AIWerkstatt/SensorBox/1-CAD/CAD.odt

CAD Design

Our instructions are intended to be used with our YouTube videos that illustrate the different steps. For the CAD Design watch: “ (https://youtu.be/I4eepCoYUTw)How to build the SensorBox – 3D Print (https://youtu.be/I4eepCoYUTw)” (https://youtu.be/I4eepCoYUTw).

We used FreeCAD (https://www.freecadweb.org/) for the design of our SensorBox. We saved our CAD designs in the folder Design in FreeCAD’s native .FCStd file format. Designs for re-use were exported and imported as .step files. We exported our designs as .stl files into the folder STL-files for 3D printing.

# FreeCAD

Take a look at the software setup section for how to set up your host computer.

Download FreeCAD

Firefox: https://www.freecadweb.org/

> Click Download now

> Click Linux 64-Bit AppImage

~/Download/FreeCAD_0.18-16146-rev1-Linux-Conda_Py3Qt5_glibc2.12-x86_64.AppImage

Ubuntu: Right-Click on FreeCAD_0.18-16146-rev1-Linux-Conda_Py3Qt5_glibc2.12-x86_64.AppImage and select Properties

> Select Permissions

> Check Allow executing file as program

An already downloaded copy can be found here:

sw/FreeCAD_0.18-16146-rev1-Linux-Conda_Py3Qt5_glibc2.12-x86_64.AppImage

Run FreeCAD

Ubuntu: Double-Click on sw/FreeCAD_0.18-16146-rev1-Linux-Conda_Py3Qt5_glibc2.12-x86_64.AppImage

# Design

The design consists of two (2) major components: a) sensors & processing board with (almost) all the electronics and b) the cover that includes an integrated display, a power button and connectors. The cover slides over the sensors & processing board and is fixed with two screws in the front (top of the vision board).

The design is very modular, and as we provide the CAD design files, it should be easy to make any design changes you desire, like using different cameras by just making small changes to the vision board.

We designed a system of grooves to join all the walls of the SensorBox. This way the walls pull themselves tightly together and the entire structure supports itself, allowing the walls to be permanently attached with just a little bit of super glue. Note that gluing pieces that have been 3D printed with PETG filament can otherwise become more challenging. The grooves were also designed so that the walls could be separated easily by just over-bending the joints.

All screws are metric and threaded heat inserts are used. The screw stands for the sensors have been designed so that they can be used with boards of any thickness.

## Sensors & Processing Board

The sensors & processing board includes: a) a bottom plate, b) a screw-on battery stand for a Poweradd Power Bank (https://www.amazon.com/gp/product/B015VXJL2S/ref=ppx_yo_dt_b_asin_title_o08_s00?ie=UTF8&psc=1) (which is also used as the central support structure for other boards) which is fixed to the bottom plate (as close as possible to the center to keep the SensorBox balanced), c) a screw-on sensor board for a SparkFun (https://www.sparkfun.com/) RedBoard Turbo Development Board (https://www.sparkfun.com/products/14812) and a suite of screw-on sensors: SparkFun NEO-M9N GPS (https://www.sparkfun.com/products/15733), SparkFun ICM20948 9DoF IMU (https://www.sparkfun.com/products/15335), SparkFun LPS25HB Pressure Sensor (https://www.sparkfun.com/products/14767) and SparkFun TMP (https://www.sparkfun.com/products/16304)102 (https://www.sparkfun.com/products/16304)Temperature Sensor (https://www.sparkfun.com/products/16304), which is fixed to the top of the battery stand, d) a screw-on power board for a SparkFun USB-C Power Delivery Board (https://www.sparkfun.com/products/15176) and a SparkFun Current and Voltage Sensor (https://www.sparkfun.com/products/15176) which is fixed upside-down just under the sensor board, e) a screw-on processor board for a NVIDIA Jetson (https://www.nvidia.com/en-us/autonomous-machines/embedded-systems/jetson-xavier-nx/)Xavier NX development kit (https://www.nvidia.com/en-us/autonomous-machines/embedded-systems/jetson-xavier-nx/) which is fixed on the side of the battery stand, exposing the fan to the right side and f) a screw-on vision board with a suite of screw-on vision sensors: two (2) Arducam S (https://www.arducam.com/product/b0191-arducam-imx219-visible-light-fixed-focus-camera-module-nvidia-jetson-nano-raspberry-pi-compute-module/)ony (https://www.arducam.com/product/b0191-arducam-imx219-visible-light-fixed-focus-camera-module-nvidia-jetson-nano-raspberry-pi-compute-module/)IMX219 Camera Modul (https://www.arducam.com/product/b0191-arducam-imx219-visible-light-fixed-focus-camera-module-nvidia-jetson-nano-raspberry-pi-compute-module/)es (https://www.arducam.com/product/b0191-arducam-imx219-visible-light-fixed-focus-camera-module-nvidia-jetson-nano-raspberry-pi-compute-module/) with two (2) SparkFun LSM9DS1 9DOF IMU (https://www.sparkfun.com/products/13944)s and two (2) SparkFu (https://www.sparkfun.com/products/14495)n (https://www.sparkfun.com/products/14495)Quiic (https://www.sparkfun.com/products/14495)A (https://www.sparkfun.com/products/14495)dapter (https://www.sparkfun.com/products/14495)s (https://www.sparkfun.com/products/14495), an Intel Realsense D (https://www.intelrealsense.com/depth-camera-d435i/)435i (https://www.intelrealsense.com/depth-camera-d435i/) RGB-D camera with a support plate, a FLIR L (https://store.groupgets.com/collections/frontpage/products/flir-lepton-3-5)epton 3.5 (https://store.groupgets.com/collections/frontpage/products/flir-lepton-3-5) thermal camera with a GroupGets P (https://store.groupgets.com/products/purethermal-2)ureTermal 2 FLIR Lepton Smart I/O Module (https://store.groupgets.com/products/purethermal-2) and a SparkFun (https://www.sparkfun.com/products/11309) (https://www.sparkfun.com/products/11309)U (https://www.sparkfun.com/products/11309)ltrasonic (https://www.sparkfun.com/products/11309)R (https://www.sparkfun.com/products/11309)ange (https://www.sparkfun.com/products/11309)F (https://www.sparkfun.com/products/11309)inder (https://www.sparkfun.com/products/11309).

The battery stand is sized slightly larger to accommodate different power banks.

All plugs and cables are located in the back, where the inclined display provides some extra room. On the left side of the battery is a passage for cables to the vision board. The bottom plate allows to attach a support for the SensorBox. The bottom plate also has a small opening for a screwdriver to help with sliding the cover off the sensors & processing board (as they hold nicely together).

The power board, the processor board, the sensor board and the vision board (mounted on the bottom plate) can be used by themselves as breadboards in early development.

We used the CAD design of the I (https://dev.intelrealsense.com/docs/cad-files)ntel RealSense Depth Camera D435 (https://dev.intelrealsense.com/docs/cad-files) to design the cutout for the Intel RealSense D435i RGB-D depth camera.

## Cover

The cover includes: a) a back wall, d) a display wall for an UCTRONICS 5 inch touch (https://www.uctronics.com/index.php/uctronics-5-inch-touch-screen-for-raspberry-pi.html) display (https://www.uctronics.com/index.php/uctronics-5-inch-touch-screen-for-raspberry-pi.html), c) two (2) side walls that provide air holes for ventilation, one for the NVIDIA Jetson NX fan (right side) and the other as exhaust (left side), three (3) keystone inserts (left side) that can be used with any keystone connector, and in our case with direct-through connectors for USB-C (https://www.amazon.com/gp/product/B078495TVK/ref=ppx_yo_dt_b_asin_title_o01_s03?ie=UTF8&psc=1) (power), HDMI (https://www.amazon.com/gp/product/B005VKKB7Q/ref=ppx_yo_dt_b_asin_title_o01_s01?ie=UTF8&psc=1) (external monitor) and USB (https://www.amazon.com/gp/product/B078935SFG/ref=ppx_yo_dt_b_asin_title_o01_s02?ie=UTF8&psc=1) (connection to NVIDIA Jetson Xavier NX), and a hole for a power button (https://www.sparkfun.com/products/11967) (right), and d) a top wall. The cover can be assembled by just sliding all the walls into each other.

aiWerkstatt (http://www.aiwerkstatt.com/)TM SensorBoxTM v1.0 2/2
