AIWerkstatt/SensorBox/4-Setup/sw/SparkFun_RedBoard_Turbo/ArduinoIDE/arduino-1.8.13-linux64/arduino-1.8.13/examples/02.Digital/toneMultiple/schematic.png

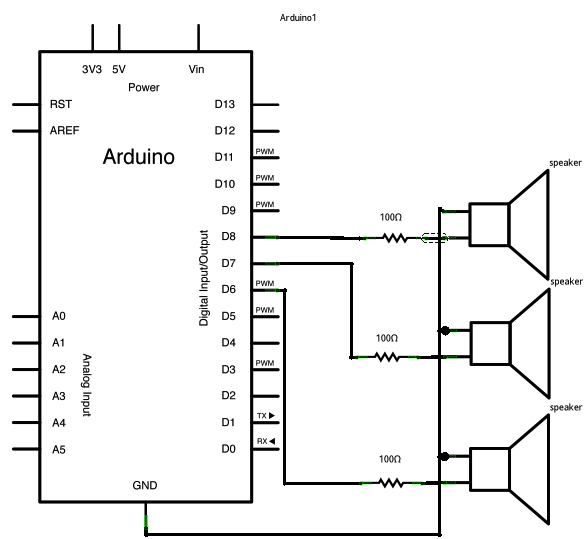
4-Setup/sw/SparkFun_RedBoard_Turbo/ArduinoIDE/arduino-1.8.13-linux64/arduino-1.8.13/examples/02.Digital/toneMultiple/schematic.png
