AIWerkstatt/SensorBox/1-CAD/Design/Cover/Side_Wall_Left.FCStd

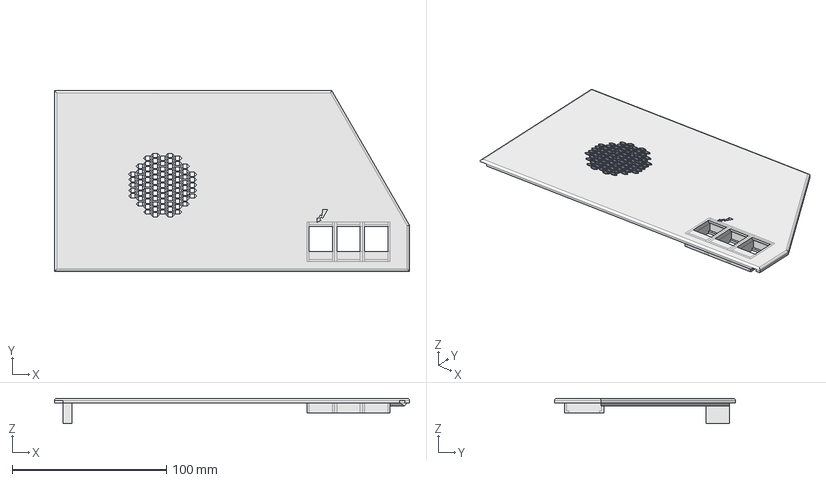
[picture p45: CAD file, 2021-07-18]
1-CAD/Design/Cover/Side_Wall_Left.FCStd
230.0 x 117.2 x 16.5 mm
