AIWerkstatt/SensorBox/1-CAD/Design/Sensors & Processing Board/Vision_Board.FCStd

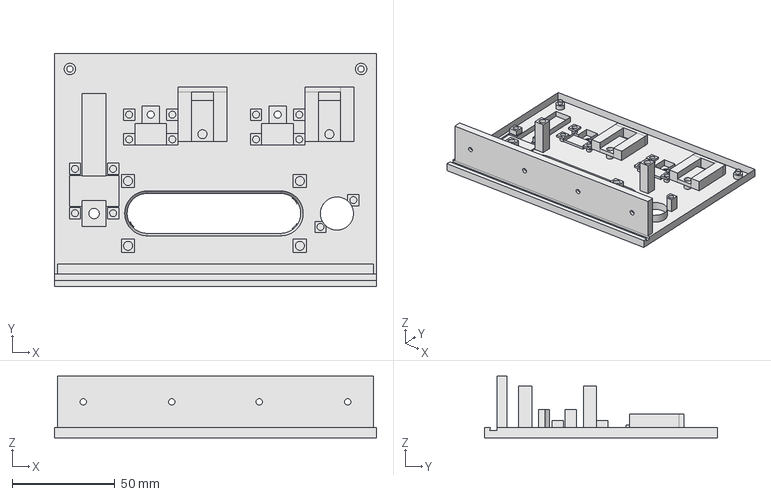
[picture p46: CAD file, 2021-07-18]
1-CAD/Design/Sensors & Processing Board/Vision_Board.FCStd
156.5 x 113.2 x 30.0 mm
