AIWerkstatt/SensorBox/1-CAD/STL-files/Display_Wall.stl

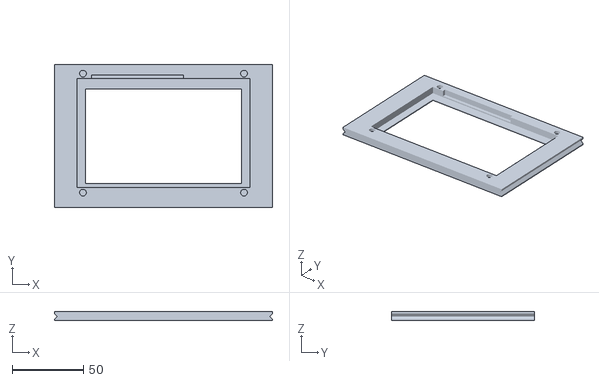
[picture p47: CAD file, 2021-07-18]
1-CAD/STL-files/Display_Wall.stl
153.5 x 100.7 x 6.50
