AIWerkstatt/SensorBox/1-CAD/Design/Cover/Display_Wall_Groove_Railing_Triangle_w3.9xd2xl100.7.step

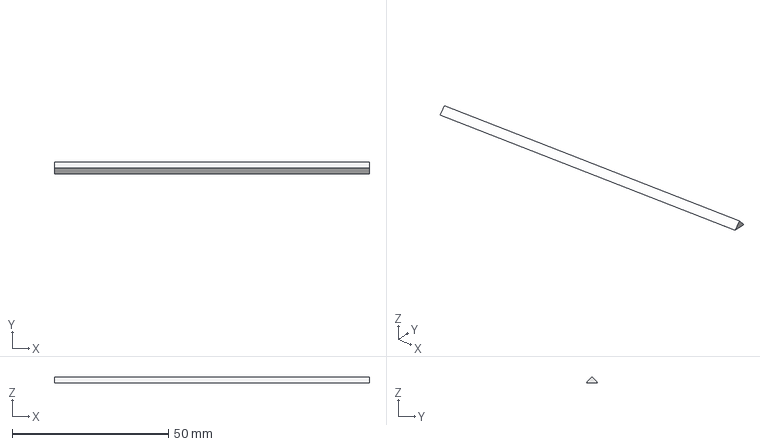
[picture p48: CAD file, 2021-07-18]
1-CAD/Design/Cover/Display_Wall_Groove_Railing_Triangle_w3.9xd2xl100.7.step
100.7 x 3.90 x 2.00 mm
