AIWerkstatt/SensorBox/1-CAD/Design/Sensors & Processing Board/Sensor_Board.FCStd

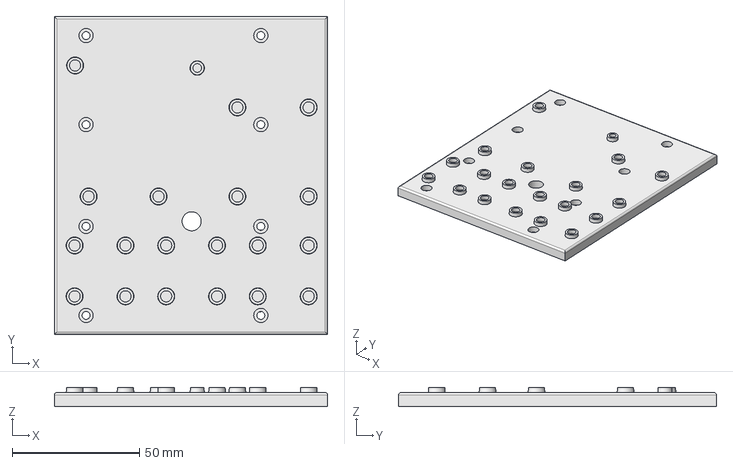
[picture p49: CAD file, 2021-07-18]
1-CAD/Design/Sensors & Processing Board/Sensor_Board.FCStd
107.5 x 125.0 x 7.50 mm
