AIWerkstatt/SensorBox/1-CAD/Design/Cover/Back_Wall.FCStd

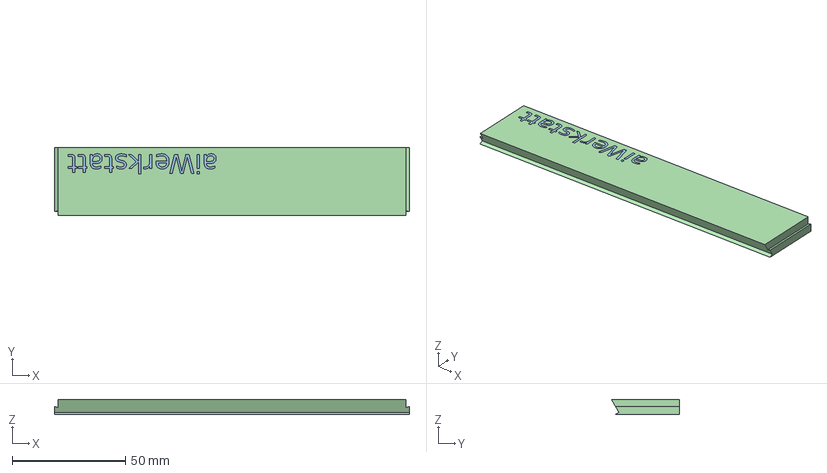
[picture p50: CAD file, 2021-07-18]
1-CAD/Design/Cover/Back_Wall.FCStd
156.5 x 30.0 x 6.50 mm
Back Wall
ShapeString
Back Wall with Name
