AIWerkstatt/SensorBox/1-CAD/STL-files/Back_Wall.stl

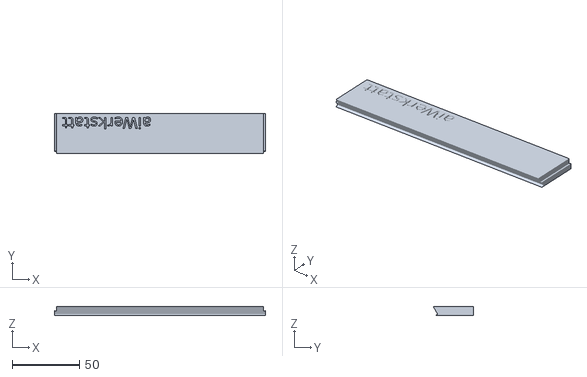
[picture p51: CAD file, 2021-07-18]
1-CAD/STL-files/Back_Wall.stl
156.5 x 30.0 x 6.50
