AIWerkstatt/SensorBox/4-Setup/sw/NVIDIA_Jetson_Xavier_NX/Intel_RealSense_D435i/librealsense/examples/C/color/readme.md

# rs-color Sample

## Overview
This sample demonstrates how to use C API to stream color data and prints some frame information such as frame number, timestamp, time of arrival, timestamp domain and a first 10 bytes of the frame data.
