AIWerkstatt/SensorBox/4-Setup/sw/NVIDIA_Jetson_Xavier_NX/Intel_RealSense_D435i/librealsense/wrappers/opencv/rotate-pointcloud/readme.md

# rs-rotate-ps sample

## Overview
This example shows how to rotate point cloud before colorization.
Current examples requires OpenCV.

## Usage:
    - press 'c' for change mode
    - press 'q' for exit

## Examples:
1. Ordinary colorization

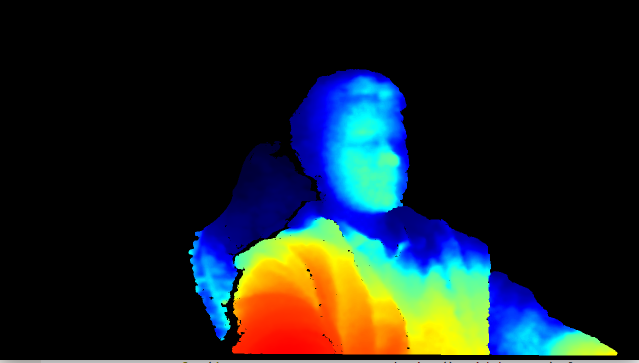
[picture p78: 4-Setup/sw/NVIDIA_Jetson_Xavier_NX/Intel_RealSense_D435i/librealsense/wrappers/opencv/rotate-pointcloud/res/front.png]


2. Rotate point cloud by roll angle for 90 degrees

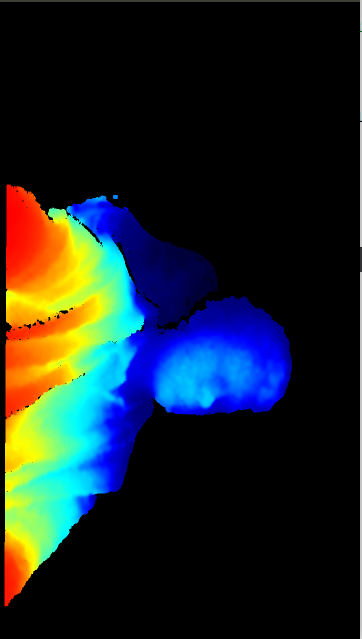
[picture p79: 4-Setup/sw/NVIDIA_Jetson_Xavier_NX/Intel_RealSense_D435i/librealsense/wrappers/opencv/rotate-pointcloud/res/roll_90.png]


3. Rotate point cloud by yaw angle for 90 degrees

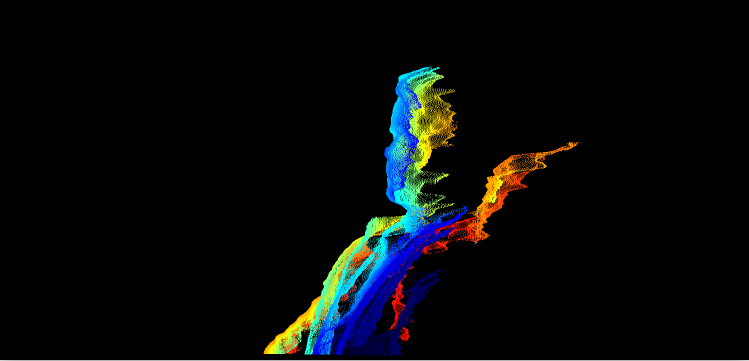
[picture p80: 4-Setup/sw/NVIDIA_Jetson_Xavier_NX/Intel_RealSense_D435i/librealsense/wrappers/opencv/rotate-pointcloud/res/yaw_90.png]
