AIWerkstatt/SensorBox/4-Setup/3.6 SparkFun NEO-M9N GPS.odt

SparkFun NEO-M9N GPS

We use the SparkFun (https://www.sparkfun.com/) NEO-M9 (https://www.sparkfun.com/products/15733)N GPS (https://www.sparkfun.com/products/15733) as our GNSS receiver. The NEO-M9N GNSS module is manufactured by u-box (https://www.u-blox.com/en).

u-blox (https://www.u-blox.com/en) published a comprehensive guide GPS Essentials of Satellite Navigation Compendium (https://www.u-blox.com/en/ubx-viewer/view/GPS-Compendium_Book_(GPS-X-02007)) for a good foundation on how Satellite Navigation works. u-blox provides u-center (https://www.u-blox.com/en/product/u-center), a free software tool under Windows (user guide (https://www.u-blox.com/sites/default/files/u-center_Userguide_%28UBX-13005250%29.pdf)), for interfacing to and configuring their GNSS receivers. u-blox provides an integration manual (https://www.u-blox.com/en/docs/UBX-19014286) for a detailed description of their GNSS receiver. u-blox provides a detailed interface document (https://www.u-blox.com/en/docs/UBX-19035940) for interfacing with their GNSS receiver, including NMEA, RTCM and u-blox’s proprietary UBX binary interface.

SparkFun provides a Hookup Guide for the SparkFun NEO-M9N GPS (https://learn.sparkfun.com/tutorials/sparkfun-gps-neo-m9n-hookup-guide).

# u-blox Firmware

u-blox provides u-center (https://www.u-blox.com/en/product/u-center), a free software tool under Windows (user guide (https://www.u-blox.com/sites/default/files/u-center_Userguide_%28UBX-13005250%29.pdf)), to update the firmware on the GNSS module.

SparkFun provides tutorials on Getting Started with U-Center for u-blox (https://learn.sparkfun.com/tutorials/getting-started-with-u-center-for-u-blox/all) and how to upgrade firmware of a u-blox GNSS receiver (https://learn.sparkfun.com/tutorials/how-to-upgrade-firmware-of-a-u-blox-gnss-receiver/all).

U-center requires the use of a Windows computer. Connect a USB to USB-C cable from the Windows computer to the USB-C port of the SparkFun NEO-M9N GPS.

Installation u-center on the Windows computer

Firefox: https://www.u-blox.com/en/product/u-center

> Click on u-center for Windows v.21.05

> Save

~/Downloads/u-center_v21.05.exe

> Double-click u-center_v21.05.exe

> Double-click u-center_v21.05

Check firmware version

> Launch u-center

> Select Receiver>Connection> COM <x>

Receiver Port <> icon turns green

> Select View>Messages View

> Select UBX>MON (Monitor)>VER (Version)

FWVER=SPG 4.0.3

Download firmware

Firefox: https://www.u-blox.com/en/product/neo-m9n-module

> Click Documentation & resources

> Click M9 SPG 4.0.4 firmware Link Download

> Save File

~/Downloads/JU_EXT_404…..bin

Upgrade firmware

> Launch u-center

> Select Receiver>Connection> COM <x>

Receiver Port <> icon turns green

> Select Tools>Firmware Update ...

> Enter Firmware image: ~/Downloads/JU_EXT_404…..bin

> Click GO (bottom left)

Firmware Update Success

# Arduino IDE

We use the SparkFun u-blox (https://github.com/sparkfun/SparkFun_u-blox_GNSS_Arduino_Library) (https://github.com/sparkfun/SparkFun_u-blox_GNSS_Arduino_Library)GNSS Arduino (https://github.com/sparkfun/SparkFun_u-blox_GNSS_Arduino_Library)Library (https://github.com/sparkfun/SparkFun_u-blox_GNSS_Arduino_Library).

Open Arduino IDE

$: sudo arduino

> Select Sketch>Include Library>Manage Libraries…

> Select SparkFun u-blox GNSS Arduino Libray

> Click 2.0.7 Install

$: sudo chmod -R +666 /opt/SparkFun_RedBoard_Turbo

An already downloaded copy of the SparkFun u-blox GNSS library (used by installation script and Dockerfile) can be found here:

sw/SparkFun_RedBoard_Turbo/SparkFun_NEO-M9N_GPS/SparkFun_u-blox_GNSS_Arduino_Library-master.zip

The library is installed under

/opt/SparkFun_RedBoard_Turbo/Arduino/libraries/SparkFun_u-blox_GNSS_Arduino_Library.

# Read GNSS

We communicate with the SparkFun NEO-M9N GPS over I2C using address 0x42.

Read GNSS

$: sudo cp -r sw/SparkFun_RedBoard_Turbo/SparkFun_NEO-M9N_GPS/read_gnss /opt/SparkFun_RedBoard_Turbo/Arduino

$: sudo chmod -R +666 /opt/SparkFun_RedBoard_Turbo

Arduino IDE

$: arduino

> File>Sketchbook>read_gnss

> Click Serial Monitor icon

> Select 115200 baud

> Click Upload icon (until flash is successful)

SparkFun NEO-M9N GPS

Current update rate: 1

Lat [degrees]: 32.96 Long [degrees]: -117.23 Alt [m]: 46.78 AltMSL [m]: 80.41 Fix: 3D Speed [m/s]: 0.86 Heading [degrees]: 281 pDOP: 3.18 SIV: 5 2021-6-21 1:16:44 Time is valid Date is valid

# Script

Run as part of the Sensor Suite installation script

sw/NVIDIA_Jetson_Xavier_NX/Scripts$ bash install-7-Sensor_Suite.sh

# Dockerfile

Part of the Sensor Suite Dockerfile

sw/NVIDIA_Jetson_Xavier_NX/Docker/Dockerfile-7-Sensor_Suite

aiWerkstatt (http://www.aiwerkstatt.com/)TM SensorBoxTM v1.0 3/3
