AIWerkstatt/SensorBox/4-Setup/3.7 ZIO INA219 Current and Voltage Sensor.odt

Zio INA219 Current and Voltage Sensor

We use the Zio INA219 Current and Voltage Sensor (https://www.sparkfun.com/products/15176) purchased through SparkFun (https://www.sparkfun.com/).

Smart Prototyping (https://www.smart-prototyping.com/) provides a Start Guide for the (https://www.smart-prototyping.com/blog/Zio-Current-and-Voltage-Sensor-Qwiic-Start-Guide)Zio Current and Voltage Sensor (https://www.smart-prototyping.com/blog/Zio-Current-and-Voltage-Sensor-Qwiic-Start-Guide).

# Arduino IDE

We use Adafruit (https://www.adafruit.com/)’s I (https://github.com/adafruit/Adafruit_INA219)NA219 Library (https://github.com/adafruit/Adafruit_INA219) and BUS IO Library (https://github.com/adafruit/Adafruit_BusIO).

Open Arduino IDE

$: sudo arduino

> Select Sketch>Include Library>Manage Libraries…

> Select Adafruit INA219

> Click 1.1.0 Install

> Click Install Adafruit INA219 only

> Select Sketch>Include Library>Manage Libraries…

> Select Adafruit Bus IO

> Click 1.7.3 Install

$: sudo chmod -R +666 /opt/SparkFun_RedBoard_Turbo

Already downloaded copies of the Adafruit INA219 and BUS IO libraries (used by installation script and Dockerfile) can be found here:

sw/SparkFun_RedBoard_Turbo/Zio_INA219_Current_and_Voltage_Sensor/Adafruit_INA219-master.zip and Adafruit_BusIO-master.zip

The libraries are installed under

/opt/SparkFun_RedBoard_Turbo/Arduino/libraries/Adafruit_INA219 and Adafruit_BusIO.

# Read Power

We communicate with the Zio INA Current and Voltage Sensor over I2C using address 0x40.

Read Power

$: sudo cp -r sw/SparkFun_RedBoard_Turbo/Zio_INA219_Current_and_Voltage_Sensor/read_power /opt/SparkFun_RedBoard_Turbo/Arduino

$: sudo chmod -R +666 /opt/SparkFun_RedBoard_Turbo

Arduino IDE

$: arduino

> File>Sketchbook>read_power

> Click Serial Monitor icon

> Select 115200 baud

> Click Upload icon (until flash is successful)

Zio INA219 Current and Voltage Sensor

Bus Voltage [V]: 19.93 Shunt Voltage [mV]: 62.64 Load Voltage [V]: 19.99 Current [mA]: 596.30 Power [mW]: 11878

# Script

Run as part of the Sensor Suite installation script

sw/NVIDIA_Jetson_Xavier_NX/Scripts$ bash install-7-Sensor_Suite.sh

# Dockerfile

Part of the Sensor Suite Dockerfile

sw/NVIDIA_Jetson_Xavier_NX/Docker/Dockerfile-7-Sensor_Suite

aiWerkstatt (http://www.aiwerkstatt.com/)TM SensorBoxTM v1.0 2/2
