AIWerkstatt/SensorBox/3-Assembly/Assembly.odt

Hardware Assembly

Our instructions are intended to be used with our YouTube videos that illustrate the different steps. For the hardware assembly watch: “How to build the SensorBox – Hardware Assembly” (https://youtu.be/YVdE3CcMVT8).

# Sensors & Processing Board

We have broken down the assembly of the Sensors & Processing Board into three (3) subsequent steps: 1 Prepare (solder, ...), 2 Attach (screws, ...) and 3 Wire (USB, Qwiic, jumper cables, ...). At each step, go through all components before moving to the next step. Some wiring is done more conveniently during earlier steps, which we identify with the step number, like 2 Wire.

## Bottom Plate

1 Prepare: Stick four (4) self-adhesive pads (https://www.acehardware.com/departments/home-and-decor/cabinet-and-furniture-hardware/protective-furniture-pads/5044524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) to the underside of the bottom plate.

2 Attach: Insert sixteen (16) M3x4 (https://www.amazon.com/gp/product/B07VH4BKBR/ref=ppx_yo_dt_b_asin_title_o04_s00?ie=UTF8&psc=1)x5 (https://www.amazon.com/gp/product/B07VH4BKBR/ref=ppx_yo_dt_b_asin_title_o04_s00?ie=UTF8&psc=1) threaded heat inserts (https://www.amazon.com/gp/product/B07VH4BKBR/ref=ppx_yo_dt_b_asin_title_o04_s00?ie=UTF8&psc=1) with a soldering iron (https://www.amazon.com/gp/product/B06XZ31W3M/ref=ppx_yo_dt_b_asin_title_o08_s00?ie=UTF8&psc=1) into all the holes on both sides of the bottom plate.

## Vision Board

2 Attach: Slide the Vision Board from the side on to the front of the Bottom Plate. If this is difficult, sand the grooves a little bit. Use four (4) M3x (https://www.amazon.com/gp/product/B00W8YSCIS/ref=ppx_yo_dt_b_asin_title_o07_s01?ie=UTF8&psc=1)6 (https://www.amazon.com/gp/product/B00W8YSCIS/ref=ppx_yo_dt_b_asin_title_o07_s01?ie=UTF8&psc=1) screws (https://www.amazon.com/gp/product/B00W8YSCIS/ref=ppx_yo_dt_b_asin_title_o07_s01?ie=UTF8&psc=1) to attach the Vision Board to the Bottom Plate.

FLIR Lepton 3.5 Thermal Camera with GroupGets Pure Thermal 2

1 Prepare: Make sure that the FLIR Lepton 3.5 (https://store.groupgets.com/collections/frontpage/products/flir-lepton-3-5) is pushed well into its socket on the GroupGets Pure Thermal 2 (https://store.groupgets.com/products/purethermal-2).

2 Attach: Insert four (4) M2x4 (https://www.amazon.com/gp/product/B0784VYCYY/ref=ppx_yo_dt_b_asin_title_o06_s00?ie=UTF8&psc=1)x3.5 (https://www.amazon.com/gp/product/B0784VYCYY/ref=ppx_yo_dt_b_asin_title_o06_s00?ie=UTF8&psc=1) threaded heat inserts (https://www.amazon.com/gp/product/B0784VYCYY/ref=ppx_yo_dt_b_asin_title_o06_s00?ie=UTF8&psc=1) into the holes of the GroupGets Pure Thermal 2 stands on the Vision Board. Use four (4) M2x (https://www.amazon.com/gp/product/B01B1OD83Y/ref=ppx_yo_dt_b_asin_title_o00_s00?ie=UTF8&psc=1)4 (https://www.amazon.com/gp/product/B01B1OD83Y/ref=ppx_yo_dt_b_asin_title_o00_s00?ie=UTF8&psc=1) (https://www.amazon.com/gp/product/B01B1OD83Y/ref=ppx_yo_dt_b_asin_title_o00_s00?ie=UTF8&psc=1)screws (https://www.amazon.com/gp/product/B01B1OD83Y/ref=ppx_yo_dt_b_asin_title_o00_s00?ie=UTF8&psc=1) to attach the GroupGets Pure Thermal 2 to its stands on the Vision Board. If the threaded heat inserts do not line up perfectly with the holes, use the soldering iron to adjust them.

3 Wire: Connect the USB cable from the GroupGets Pure Thermal 2 to a USB port on the NVIDIA Jetson Xavier NX Development Board.

MaxBotix HRLV-MaxSonar-EZ4 Ultrasonic Range Finder

1 Prepare: Solder Break Away Headers (https://www.sparkfun.com/products/116) to all seven (7) pins on the MaxBotix HRLV-MaxSonar-EZ4 Ultrasonic Range Finder (https://www.sparkfun.com/products/11309). Solder the TTL jumper on the MaxBotix HRLV-MaxSonar-EZ4 Ultrasonic Range Finder to enable TTL on pin 5 (inversion of default provided RS232 signal).

2 Attach: Insert two (2) M2x4x3.5 threaded heat inserts into the holes of the MaxBotix HRLV-MaxSonar-EZ4 Ultrasonic Range Finder stands on the Vision Board. Sand or file away the part of the stand that interferes with the header. Use two (2) M2x4 screws to attach the MaxBotix HRLV-MaxSonar-EZ4 Ultrasonic Range Finder to its stands on the Vision Board.

3 Wire: Connect the GND (pin 7), V+ (pin 6) and the Serial TTL TX (pin 5) of the MaxBotix HRLV-MaxSonar-EZ4 Ultrasonic Range Finder to the GND (pin GND), V3.3 (pin 3V3) and the UART RX (pin RX/D0) of the SparkFun RedBoard Turbo Development Board using three (3) 20cm male - female jumper wires (https://www.amazon.com/Elegoo-EL-CP-004-Multicolored-Breadboard-arduino/dp/B01EV70C78) (black for GND, red for V+ and green for Serial TTL). The UART TX (pin TX/D1) is not and shall not be used.

Intel RealSense D435i RGB-D Camera

2 Attach: Insert four (4) M3x6 (https://www.amazon.com/gp/product/B087NBYF65/ref=ppx_yo_dt_b_asin_title_o07_s01?ie=UTF8&psc=1)x4.5 (https://www.amazon.com/gp/product/B087NBYF65/ref=ppx_yo_dt_b_asin_title_o07_s01?ie=UTF8&psc=1) threaded heat inserts (https://www.amazon.com/gp/product/B087NBYF65/ref=ppx_yo_dt_b_asin_title_o07_s01?ie=UTF8&psc=1) into the holes of the Intel RealSense D435i stands on the Vision Board. Use two (2) M3x (https://www.amazon.com/gp/product/B01C3LHQ0K/ref=ppx_yo_dt_b_asin_title_o08_s00?ie=UTF8&psc=1)5 (https://www.amazon.com/gp/product/B01C3LHQ0K/ref=ppx_yo_dt_b_asin_title_o08_s00?ie=UTF8&psc=1) screws (https://www.amazon.com/gp/product/B01C3LHQ0K/ref=ppx_yo_dt_b_asin_title_o08_s00?ie=UTF8&psc=1) to attach the Intel RealSense D435i (https://www.intelrealsense.com/depth-camera-d435i/) to the Intel RealSense D435i support. Use four (4) M3x6 screws to attach the Intel RealSense D435i support to its stands on the Vision Board.

3 Wire: Connect the USB cable from the Intel RealSense D435i to a USB port on the NVIDIA Jetson Xavier NX Development Board.

Arducam Sony IMX219 Rolling Shutter RGB Cameras

1 Prepare: Change the FPC 15 pin ribbon cables from the two (2) Arducam Sony IMX219 camera modules (https://www.uctronics.com/arducam-8-mp-sony-visible-light-ir-fixed-focus-camera-module-for-nvidia-jetson-nano.html) against two (2) 30cm long FPC 15 pin ribbon cables (https://www.amazon.com/gp/product/B089LM5D1T/ref=ppx_yo_dt_b_asin_title_o04_s00?ie=UTF8&psc=1). Carefully lift up the plastic tab, that holds the ribbon cable in place. Pull out the ribbon cable and push in the new ribbon cable. Press down on the plastic tab to fix the ribbon cable. Take off the lens protection film.

2 Attach: Insert eight (8) M2x4x3.5 threaded heat inserts into the holes of the two (2) Arducam Sony IMX219 stands on the Vision Board. Use eight (8) M2x4 screws to attach the two (2) Arducam Sony IMX219s to their stands on the Vision Board.

3 Wire: Connect the FPC 15 pin ribbon cables from the two (2) Arducam Sony IMX219 camera modules through the holes in the Processing Board to the MIPI-CSI connectors on the NVIDIA Jetson Xavier NX Development Board. Carefully lift up the plastic tab, that holds the ribbon cable in place. Push in the ribbon cable (blue side outside / contacts inside). Press down on the plastic tab to fix the ribbon cable.

Optional: SparkFun LSM9DS1 IMUs

We are going to connect the two (2) SparkFun LSM9DS1 (https://www.sparkfun.com/products/13944)IMU (https://www.sparkfun.com/products/13944)s using two (2) SparkFun Qwicc Adapters to the SparkFun RedBoard Turbo Development Board. Alternatively, as the Arducam Sony IMX219 are connect to the NVIDIA Jetson Xavier NX Development Board, we can also connect the SparkFun LSM9DS1 IMU to the NVIDIA Jetson Xavier NX Development Board.

1 Prepare: With a soldering iron, solder Break Away Headers (https://www.sparkfun.com/products/116) to the four (4) I2C pins on the two (2) SparkFun LSM9DS1 IMUs. The header should be pointing up from the board to be later connected to the SparkFun Qwiic Adapters. As we use two (2) SparkFun LSM9DS1 IMUs we need to change the I2C addresses of one of them. Take one of them and use a Carving Craft Knife (https://www.amazon.com/Mlife-Precision-Carving-Stainless-Cutting/dp/B074P34MFB) to cut the trace between the center and the top pads of the MAG and ACC/GYR jumpers and use solder to short the center and bottom pads to change the address of the magnetometer to 0x1C and the accelerometer and gyroscope to 0x6A.

2 Attach: Insert two (2) M3x6x4.5 threaded heat inserts into the holes of the two (2) SparkFun LSM9DS1 IMUs stands on the Vision Board. Use two (2) M3x6 screws to attach the two (2) SparkFun LSM9DS1 IMUs to their stands on the Vision Board. Place the one with the alternative I2C addresses to the right (seen from the inside).

Optional: SparkFun Qwiic Adapters

1 Prepare: Place the two (2) SparkFun LSM9DS1 IMUs into their locations on the Vision Board. Place the two (2) SparkFun Qwiic Adapter (https://www.sparkfun.com/products/14495)s on the Break Away Headers on the SparkFun LSM9DS1 IMUs. Solder the Break Away Headers to the SparkFun Qwiic Adapters.

2 Wire: Connect the two (2) SparkFun Qwiic Adapters to the Qwiic I2C daisy-chain from the SparkFun RedBoard Turbo Development Board. Connect the two (2) SparkFun Qwiic Adapters with a 5 (https://www.sparkfun.com/products/15081)0mm Qwiic cable (https://www.sparkfun.com/products/15081) and the right SparkFun Qwiic Adapter with a 100mm Qwiic cable (https://www.sparkfun.com/products/15081) to the SparkFun TMP 102 Temperature Sensor.

## Battery

2 Attach: Insert sixteen (16) M3x4x5 threaded heat inserts into all the holes on the top (for the Sensor Board) and on the back (for the Processing Board) on the four (4) Battery Stands. Use eight (8) M3x6 screws to attach the Battery Stands to the top of the Bottom Plate. The holes for the Processing Board should face to the right side (looking at the bottom plate from where you can read the text). Insert two (2) 14 inch zip ties (https://www.acehardware.com/departments/lighting-and-electrical/cable-management-cable-ties-and-electrical-tape/cable-ties/34807) into the Battery Stands, from the top left, to top right, to the bottom right, and then back to the bottom left. Insert the tip (only a few mm) into the head and then pull in the head tight to the Battery Stand. Push the USB-C p (https://www.amazon.com/gp/product/B015VXJL2S/ref=ppx_yo_dt_b_asin_title_o08_s00?ie=UTF8&psc=1)ower bank (https://www.amazon.com/gp/product/B015VXJL2S/ref=ppx_yo_dt_b_asin_title_o08_s00?ie=UTF8&psc=1) in the Battery Stand through the zip ties so that the front of the USB-C power bank with the connectors faces the back of the Bottom Plate (where the text is). If the USB-C power bank is smaller than the provided space, use double sided tape to make it fit snug. Tighten up the zip ties. You should be able to swing the Bottom Plate with the USB-C power bank around without that the power bank moves. Cut off the ends of the zip ties.

## Power Board

2 Attach: Do part of the 2 Attach step of the Sensor Board (next component) first. Use two (2) M3x6 screws to attach the Power Board to the bottom side of the Sensor Board.

SparkFun USB-C Power Delivery Board

1 Prepare: Solder a 2 pin Screw Terminal Block Connector (https://www.amazon.com/gp/product/B07B791NMQ/ref=ppx_yo_dt_b_asin_title_o00_s00?ie=UTF8&psc=1) to the VSNK and GND pins on the SparkFun USB-C Power Delivery Board. Take a look at the USB-C Power Delivery part in the software setup section and set up the power delivery of the SparkFun USB-C (https://www.sparkfun.com/products/15801)Power Delivery Board (https://www.sparkfun.com/products/15801) to provide power for the NVIDIA Jetson Xavier NX (https://www.nvidia.com/en-us/autonomous-machines/embedded-systems/jetson-xavier-nx/).

2 Attach: Insert four (4) M3x6x4.5 threaded heat inserts into the holes of the M3x6 stands for the SparkFun USB-C Power Delivery Board on the Power Board. Use four (4) M3x6 screws to attach the SparkFun USB-C Power Delivery Board to its stands on the Power Board.

2 Wire: Connect the USB-C power bank with the USB-C male to male 100W power cable (https://www.amazon.com/gp/product/B08816SYKY/ref=ppx_yo_dt_b_asin_title_o09_s02?ie=UTF8&psc=1) to the SparkFun USB-C Power Delivery Board. Use a multimeter (https://www.sparkfun.com/products/12966) to measure 20V between the VSNK and GND pins (connected to the terminal block) on the SparkFun USB-C Power Delivery Board.

ZIO INA219 Current and Voltage Sensor

2 Attach: Insert four (4) M3x6x4.5 threaded heat inserts into the holes of the ZIO INA (https://www.sparkfun.com/products/15176)219 (https://www.sparkfun.com/products/15176) (https://www.sparkfun.com/products/15176)Current and Voltage Sensor (https://www.sparkfun.com/products/15176) stands on the Power Board. Use four (4) M3x6 screws to attach the ZIO INA219 Current and Voltage Sensor to its stands on the Power Board.

2: Wire: Stripe the ends of an about 30mm long red 22AGW (https://www.sparkfun.com/products/11367) wire with a wire stripper (https://www.sparkfun.com/products/14762). Connect the + pole of the screw terminal on the SparkFun USB-C Power Delivery board to the – pole of the screw terminal on the ZIO INA219 Current and Voltage Sensor. Connect a 200mm (https://www.sparkfun.com/products/15081)Qwi (https://www.sparkfun.com/products/15081)i (https://www.sparkfun.com/products/15081)c cable (https://www.sparkfun.com/products/15081) to the Qwiic connector on the ZIO INA219 Current and Voltage Sensor and slide the other end of the cable through the hole in the Power Board.

DC Barrel Jack Connector

2: Wire: Stripe the ends of a 270mm long red, a 460mm long red and a 230mm black 22AGW wire with a wire stripper. Crimp a male and a female quick disconnect terminal connector (https://www.amazon.com/gp/product/B01EE3QGG0/ref=ppx_yo_dt_b_asin_title_o05_s01?ie=UTF8&psc=1) with a crimper (https://www.amazon.com/IWISS-SN-28B-Crimping-AWG28-18-Dupont/dp/B00OMM4YUY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) to the ends of one side of the red wires. These quick connectors will be connected to the quick connectors connected to the push button in the cover when the cover is put on. Using a male and female connector allows to short-cut the wires easily so that the push button is not required to power the SensorBox. Put two (2) red heat shrink tube (just preparation, no heat) over the red wires to join them together, and two (2) black heat shrink tubes over the 270mm long red wire and the black wire. Connect one end of the black wire to the - pole of the screw terminal on the SparkFun USB-C Power Delivery board. Connect the other end of the 270mm long red wire to the – pole of the screw terminal on the ZIO INA Current and Voltage Sensor. Connect the other end of the black wire to the – pole of the DC (https://www.amazon.com/gp/product/B07DJ63MJP/ref=ppx_yo_dt_b_asin_title_o03_s00?ie=UTF8&psc=1)Barrel Jack connector (https://www.amazon.com/gp/product/B07DJ63MJP/ref=ppx_yo_dt_b_asin_title_o03_s00?ie=UTF8&psc=1). Connect the other end of the 460mm long red wire to the + pole of the DC Barrel Jack connector. Position and heat the heat shrink tubes using a heat gun (https://www.amazon.com/gp/product/B07P5WFHJ7/ref=ppx_yo_dt_b_asin_title_o05_s01?ie=UTF8&psc=1) to make them fit. Just for testing, short-cut the wires by connecting the male and female connectors. Use a multimeter to measure 20V between the inside (+ red) and the outside (black) of the DC Barrel Jack connector.

## Sensor Board

2 Attach: Before the 2 Attach step of the Power Board (previous component), insert two (2) M3x4x5 threaded heat inserts into the holes for the Power Board on the bottom of the Sensor Board. Use eight (8) M3x6 screws to attach the Sensor Board to the top side of the Battery Stands.

SparkFun RedBoard Turbo Development Board (Arduino Zero)

2 Attach: Insert three (3) M3x6x4.5 threaded heat inserts and one (1) M2x6 (https://www.amazon.com/gp/product/B0784VYCYY/ref=ppx_yo_dt_b_asin_title_o06_s00?ie=UTF8&psc=1)x3.5 (https://www.amazon.com/gp/product/B0784VYCYY/ref=ppx_yo_dt_b_asin_title_o06_s00?ie=UTF8&psc=1) threaded heat insert (https://www.amazon.com/gp/product/B0784VYCYY/ref=ppx_yo_dt_b_asin_title_o06_s00?ie=UTF8&psc=1) into the holes of the SparkFun RedBoard Turb (https://www.sparkfun.com/products/14812)o (https://www.sparkfun.com/products/14812) Development Board (https://www.sparkfun.com/products/14812) stands in the back right location on the Sensor Board. Use three (3) M3x6 screws and one (1) M2x6 screw (https://www.amazon.com/gp/product/B01FL88Y76/ref=ppx_yo_dt_b_asin_title_o07_s01?ie=UTF8&psc=1) to attach the SparkFun RedBoard Turbo Development Board to its stands on the Sensor Board. The M2 screw is used for the tiny hole on the SparkFun RedBoard Turbo Development Board close to the USB connector.

2 Wire: The sensors will be connected via a Qwiic I2C daisy-chain to the Qwiic connector on the SparkFun RedBoard Turbo Development Board. We didn’t need to, but when daisy-chaining 7x I2C devices on the same bus you may want to disable the I2C pull-up resistors, by cutting the jumpers, on some of the boards.

3 Wire: Connect the SparkFun RedBoard Turbo Development Board from its USB port with a 90° micro USB to USB cable (https://www.amazon.com/gp/product/B003YKX6WC/ref=ppx_yo_dt_b_asin_title_o01_s00?ie=UTF8&psc=1) to a USB port on the NVIDIA Jetson Xavier NX Development Board.

SparkFun TMP102 Temperature Sensor

1 Prepare: Solder a Break Away Header to the INT pin on the SparkFun TMP102 T (https://www.sparkfun.com/products/16304)emperatur (https://www.sparkfun.com/products/16304)e (https://www.sparkfun.com/products/16304)S (https://www.sparkfun.com/products/16304)ensor (https://www.sparkfun.com/products/16304).

2 Attach: Insert four (4) M3x6x4.5 threaded heat inserts into the holes of the SparkFun TMP102 Temperature Sensor stands in the front right location on the Sensor Board. Use four (4) M3x6 screws to attach the SparkFun TMP102 Temperature Sensor to its stands on the Sensor Board.

2 Wire: Connect the SparkFun TMP102 Temperature Sensor to the Qwiic I2C daisy-chain from the SparkFun RedBoard Turbo Development Board by connecting the SparkFun TMP102 Temperature Sensor with a 50mm Qwiic cable to the SparkFun RedBoard Turbo Development Board.

SparkFun ICM20948 IMU

1 Prepare: Solder Break Away Headers to the INT and FSYNC pins on the SparkFun ICM20948 IMU (https://www.sparkfun.com/products/15335).

2 Attach: Insert four (4) M3x6x4.5 threaded heat inserts into the holes of the SparkFun ICM20948 IMU stands in the front middle location on the Sensor Board. Use four (4) M3x6 screws to attach the SparkFun ICM20948 IMU to its stands on the Sensor Board.

2 Wire: Connect the SparkFun ICM20948 IMU to the Qwiic I2C daisy-chain from the SparkFun RedBoard Turbo Development Board by connecting the SparkFun ICM20948 IMU with a 100mm Qwiic cable to the left SparkFun Qwiic Adapter on the Vision Board.

SparkFun LPS25HB Pressure Sensor

1 Prepare: Solder a Break Away Header to the INT pin on the SparkFun LPS25HB P (https://www.sparkfun.com/products/14767)ressur (https://www.sparkfun.com/products/14767)e Sensor (https://www.sparkfun.com/products/14767).

2 Attach: Insert four (4) M3x6x4.5 threaded heat inserts into the holes of the SparkFun LPS25HB Pressure Sensor stands in the front left location on the Sensor Board. Use two (2) M3x6 screws to attach the SparkFun LPS25HB Pressure Sensor to its stands on the Sensor Board.

2 Wire: Connect the SparkFun LPS25HB Pressure Sensor to the Qwiic I2C daisy-chain from the SparkFun RedBoard Turbo Development Board by connecting the SparkFun LPS25HB Pressure Sensor with a 50mm Qwiic cable to the SparkFun ICM20948 IMU.

SparkFun NEO-M9N GPS

1 Prepare: Solder Break Away Headers to the PPS, RST, SAFE and INT pins on the SparkFun NEO-M9N GPS (https://www.sparkfun.com/products/15733).

2 Attach: Insert four (4) M3x6x4.5 threaded heat inserts into the holes of the SparkFun NEO-M9N GPS stands in the back left location on the Sensor Board. Use four (4) M3x6 screws to attach the SparkFun NEO-M9N GPS to its stands on the Sensor Board.

2 Wire: Connect the SparkFun NEO-M9N GPS to the Qwiic I2C daisy-chain from the SparkFun RedBoard Turbo Development Board by connecting the SparkFun NEO-M9N GPS with a 50mm Qwiic cable to the SparkFun LPS25HB Pressure Sensor and the 200mm Qwiic cable from the ZIO INA219 Current and Voltage Sensor.

## Processing Board

2 Attach: Use seven (7) M3x6 screws to attach the Processing Board to the right side of the Battery Stands.

NVIDIA Jetson Xavier NX Development Board

1 Prepare: Extract the NVIDIA Jetson Xavier (https://www.amazon.com/NVIDIA-Jetson-Xavier-Developer-812674024318/dp/B086874Q5R?hvadid=459454121958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)N (https://www.amazon.com/NVIDIA-Jetson-Xavier-Developer-812674024318/dp/B086874Q5R?hvadid=459454121958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)X Development Board (https://www.amazon.com/NVIDIA-Jetson-Xavier-Developer-812674024318/dp/B086874Q5R?hvadid=459454121958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) with its antennas of the wifi and bluetooth module from the plastic support of the development kit. Add a NVMe S (https://www.amazon.com/Samsung-970-EVO-Plus-250GB/dp/B07M7Q21N7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)SD Drive (https://www.amazon.com/Samsung-970-EVO-Plus-250GB/dp/B07M7Q21N7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) in the M.2 Key M slot to the NVIDIA Jetson Xavier NX board. On the back side of the NVIDIA Jetson Xavier NX Development Board unscrew the retaining screw in the M.2 Key M slot, push in the NVMe SSD Drive into the connector and fix it by screwing the retaining screw back in. Insert a Micro SD Card (https://www.amazon.com/Samsung-MicroSD-Adapter-MB-ME64GA-AM/dp/B06XX29S9Q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) into the Micro SD slot on the NVIDIA Jetson Xavier NX.

2 Attach: Insert four (4) M2x6 (https://www.amazon.com/gp/product/B0784VYCYY/ref=ppx_yo_dt_b_asin_title_o06_s00?ie=UTF8&psc=1)x3.5 (https://www.amazon.com/gp/product/B0784VYCYY/ref=ppx_yo_dt_b_asin_title_o06_s00?ie=UTF8&psc=1) threaded heat inserts (https://www.amazon.com/gp/product/B0784VYCYY/ref=ppx_yo_dt_b_asin_title_o06_s00?ie=UTF8&psc=1) into the holes of the M2x6 stands for the NVIDIA Jetson Xavier NX. Use eight (8) M2x6 screws (https://www.amazon.com/gp/product/B01FL88Y76/ref=ppx_yo_dt_b_asin_title_o07_s01?ie=UTF8&psc=1) to attach the NVIDIA Jetson Xavier NX Development Board with its antennas of the WiFi and Bluetooth module to the Processing Board. Place the NVIDIA Jetson Xavier NX Development Board so that the connectors face the back of the Bottom Plate.

3 Wire: Connect the DC Barrel Jack Connector to the DC Jack of the NVIDIA Jetson Xavier NX Development Board. Use double sided tape (https://www.amazon.com/gp/product/B07T1PWMTT/ref=ppx_yo_dt_b_asin_title_o00_s00?ie=UTF8&psc=1) to fix the DC Barrel Jack Connector to the Processing Board. Use a zip tie to hold the DC Barrel Jack Connector in place.

# Cover

Insert two (2) M3x4x5 threaded heat inserts into the two (2) holes on the inside in the front of the Cover, where the Vision Board will be attached.

UCTRONICS 5 Inch Touch Screen Display

Connect a 90° micro USB to USB cable (https://www.amazon.com/gp/product/B003YKX6WC/ref=ppx_yo_dt_b_asin_title_o01_s00?ie=UTF8&psc=1) to USB touch port on the UCTRONICS 5 Inch Touch Scree (https://www.uctronics.com/index.php/uctronics-5-inch-touch-screen-for-raspberry-pi.html)n Display (https://www.uctronics.com/index.php/uctronics-5-inch-touch-screen-for-raspberry-pi.html) (once the display is in the Cover, there is not enough room to get it in). This cable will be connected to a USB port on the NVIDIA Jetson Xavier NX Development Board when the Cover is put on.

As part of the 3D printing and post-processing, insert already four (4) M3x4 threaded heat inserts into the holes for the UCTRONICS 5 Inch Touch Screen Display in the Display Wall of the Cover. Use four (4) M3x5 screws (smaller than M3x6 screws) to attach the UCTRONICS 5 Inch Touch Screen Display in the Cover.

Power Push Button

Stripe the ends of two (2) about 9cm long red 22AGW wires with a wire stripper. Solder one end of the wires to the Common Ground (C) and Normally Open (NO) connections of the push button (https://www.sparkfun.com/products/11967). Protect the connections and join the cables together by fitting hea (https://www.amazon.com/gp/product/B073R69KNB/ref=ppx_yo_dt_b_asin_title_o05_s02?ie=UTF8&psc=1)t (https://www.amazon.com/gp/product/B073R69KNB/ref=ppx_yo_dt_b_asin_title_o05_s02?ie=UTF8&psc=1) (https://www.amazon.com/gp/product/B073R69KNB/ref=ppx_yo_dt_b_asin_title_o05_s02?ie=UTF8&psc=1)shrink tub (https://www.amazon.com/gp/product/B073R69KNB/ref=ppx_yo_dt_b_asin_title_o05_s02?ie=UTF8&psc=1)es (https://www.amazon.com/gp/product/B073R69KNB/ref=ppx_yo_dt_b_asin_title_o05_s02?ie=UTF8&psc=1) using a heat gun (https://www.amazon.com/gp/product/B07P5WFHJ7/ref=ppx_yo_dt_b_asin_title_o05_s01?ie=UTF8&psc=1). Crimp a male and a female quick disconnect terminal connector (https://www.amazon.com/gp/product/B01EE3QGG0/ref=ppx_yo_dt_b_asin_title_o05_s01?ie=UTF8&psc=1) with a crimper (https://www.amazon.com/IWISS-SN-28B-Crimping-AWG28-18-Dupont/dp/B00OMM4YUY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) to the other end of the wires. Assemble two (2) push buttons this way, so you have a spare push button when using the Sensors & Processing Board without the Cover.

Screw the push button into the little round hole in the back (display) on the right side of the Cover.

Connectors

Push the Keystone jacks from the inside into the Keystone inserts on the left side of the Cover in the following order from the back (display) to the front: USB (https://www.amazon.com/gp/product/B078935SFG/ref=ppx_yo_dt_b_asin_title_o01_s02?ie=UTF8&psc=1)3.0 (https://www.amazon.com/gp/product/B078935SFG/ref=ppx_yo_dt_b_asin_title_o01_s02?ie=UTF8&psc=1), HMDI (https://www.amazon.com/gp/product/B005VKKB7Q/ref=ppx_yo_dt_b_asin_title_o01_s03?ie=UTF8&psc=1) and USB-C (https://www.amazon.com/gp/product/B078495TVK/ref=ppx_yo_dt_b_asin_title_o01_s00?ie=UTF8&psc=1) (under the power sign on the Cover).

Air Holes

Cut two (2) pieces out of the PC Computer Air Filter (https://www.amazon.com/gp/product/B000FJU8BC/ref=ppx_yo_dt_b_asin_title_o01_s03?ie=UTF8&psc=1) to cover the air holes in the side walls and use some tape (https://www.amazon.com/3M-Contractor-Grade-Multi-Use-Silver/dp/B00DJWTGAG?s=industrial) to fix them from the inside.

# Sensors & Processing Board as a desktop computer

You may want to use the Sensors & Processing Board without the Cover to have full access to the system. We use the Sensors & Processing Board without the Cover for our software setup.

Connect the male and female quick disconnect terminal connectors from the spare push button to the quick disconnect terminal connectors on the wires that come from the Zio INA219 Current and Voltage Sensor and the DC Barrel Jack connector. Put the USB dongle from the Dual USB & Bluetooth Keyboard and Mouse (https://www.amazon.com/gp/product/B0899DRDYR/ref=ppx_yo_dt_b_asin_title_o07_s00?ie=UTF8&psc=1) in a USB port of the NVIDIA Jetson Xavier NX. Connect a HDMI monitor (https://www.amazon.com/Acer-SB220Q-Ultra-Thin-Frame-Monitor/dp/B07CVL2D2S?s=electronics) directly with a HDMI (https://www.amazon.com/AmazonBasics-High-Speed-HDMI-Cable-1-Pack/dp/B014I8T0YQ?s=electronics)cable (https://www.amazon.com/AmazonBasics-High-Speed-HDMI-Cable-1-Pack/dp/B014I8T0YQ?s=electronics) to the HDMI port of the NVIDIA Jetson Xavier NX Development Board.

Connect the USB-C charger (https://www.amazon.com/gp/product/B08F7NHMLB/ref=ox_sc_act_title_1?smid=A1AEYAFEWEFJJF&psc=1) directly to the PD 100W IN port of the USB-C power bank.

Push the push button to turn on the Sensorbox. If the SensorBox does not turn on, it might be that the USB-C power bank is not active. To activate the USB-C power bank, either push the button the on USB-C power bank, or (re-)connect the USB-C charger to USB-C power bank. Make sure to shutdown the Sensorbox properly from the operating system (do not just switch off the power).

To set up the SensorBox from a host computer, connect a USB port on the host computer with a Micro (https://www.amazon.com/6in-Micro-USB-Cable-6-inches/dp/B002L5ZEYY)USB (https://www.amazon.com/6in-Micro-USB-Cable-6-inches/dp/B002L5ZEYY)to USB cable (https://www.amazon.com/6in-Micro-USB-Cable-6-inches/dp/B002L5ZEYY) to the Micro USB port on the NVIDIA Jetson Xavier NX Development Board.

# Putting on the Cover

Connect a HDMI Male to Female (https://www.amazon.com/gp/product/B06WGPT999/ref=ppx_yo_dt_b_asin_title_o06_s00?ie=UTF8&psc=1)c (https://www.amazon.com/gp/product/B06WGPT999/ref=ppx_yo_dt_b_asin_title_o06_s00?ie=UTF8&psc=1)able (https://www.amazon.com/gp/product/B06WGPT999/ref=ppx_yo_dt_b_asin_title_o06_s00?ie=UTF8&psc=1) to the HDMI port of the NVIDIA Jetson Xavier NX board. Connect a DisplayPort Male to HDMI Female cable (https://www.amazon.com/gp/product/B019Q652AG/ref=ppx_yo_dt_b_asin_title_o02_s00?ie=UTF8&psc=1) to the DisplayPort of the NVIDIA Jetson Xavier NX Development Board. Connect a HDMI Male to Male cable (https://www.amazon.com/gp/product/B07KSP1SMS/ref=ppx_yo_dt_b_asin_title_o02_s00?ie=UTF8&psc=1) to the DisplayPort Male to HDMI Female cable. Connect a Micro (https://www.amazon.com/6in-Micro-USB-Cable-6-inches/dp/B002L5ZEYY)USB (https://www.amazon.com/6in-Micro-USB-Cable-6-inches/dp/B002L5ZEYY)to USB cable (https://www.amazon.com/6in-Micro-USB-Cable-6-inches/dp/B002L5ZEYY) to the Micro USB port on the NVIDIA Jetson Xavier NX Development Board. Connect a 100W U (https://www.amazon.com/gp/product/B072M7GH29/ref=ppx_yo_dt_b_asin_title_o00_s00?ie=UTF8&psc=1)SB-C (https://www.amazon.com/gp/product/B072M7GH29/ref=ppx_yo_dt_b_asin_title_o00_s00?ie=UTF8&psc=1)p (https://www.amazon.com/gp/product/B072M7GH29/ref=ppx_yo_dt_b_asin_title_o00_s00?ie=UTF8&psc=1)ower (https://www.amazon.com/gp/product/B072M7GH29/ref=ppx_yo_dt_b_asin_title_o00_s00?ie=UTF8&psc=1)c (https://www.amazon.com/gp/product/B072M7GH29/ref=ppx_yo_dt_b_asin_title_o00_s00?ie=UTF8&psc=1)able (https://www.amazon.com/gp/product/B072M7GH29/ref=ppx_yo_dt_b_asin_title_o00_s00?ie=UTF8&psc=1) to the PD 100W IN port of the USB-C power bank.

Slide the Cover over the Sensors & Processing Board until you can still see the USB connectors on the NVIDIA Jetson Xavier NX Development Board. Connect the USB cable from the UCTRONICS 5 Inch Touch Screen Display to a USB port on the NVIDIA Jetson Xavier NX Development Board.

Slide the Cover now 2/3 over the Sensors & Processing Board so you have still enough access to connect all the cables. Connect the HDMI Male to Female Cable from the NVIDIA Jetson Xavier NX Development Board to the HDMI port on the UCTRONICS 5 Inch Touch Screen Display. Connect the male and female quick disconnect terminal connectors from the wires that come from the Zio INA219 Current and Voltage Sensor and the DC Barrel Jack connector to the quick disconnect terminal connectors from the push button in the Cover. Connect the USB-C power cable from the USB-C power bank to the USB-C Keystone Jack in the Cover. Connect the HDMI Male to Male cable from the NVIDIA Jetson Xavier NX Development Board to the HDMI Keystone Jack in the Cover. Connect the Micro USB to USB cable from the NVIDIA Jetson Xavier NX Development Board to the USB 3.0 Keystone Jack in the Cover.

There seems to be a “right” sense on how to connect the USB-C cable from the USB-C charger to the USB-C Keystone Jack so that the USB-C power bank is actually charging. Make sure to test the connection and mark the “right” sense on the USB-C cable prior to putting on the cover all the way.

Slide the cover all the way over the Sensors & Processing Board. Use two (2) M3x6 screws to attach the Vision Board, which is in front of the Sensors & Processing Board, to the Cover.

The total weight of the SensorBox is 2.130kg.

# SensorBox as a desktop computer

You can hook up the SensorBox as a Desktop computer with an external monitor, keyboard and mouse.

Connect a HDMI monitor with a HDMI cable (https://www.amazon.com/AmazonBasics-High-Speed-HDMI-Cable-1-Pack/dp/B014I8T0YQ?s=electronics) to the HDMI Keystone Jack in the Cover. After software setup, the Dual USB & Bluetooth Keyboard and Mouse is connected via Bluetooth directly to the NVIDIA Jetson Xavier NX Development Board.

Connect the USB-C charger with the USB-C cable in the “right” sense to USB-C Keystone Jack in the Cover. Push the push button to turn on the Sensorbox. If the SensorBox does not turn on, it might be that the USB-C power bank is not active. To activate the USB-C power bank, (re-)connect the USB-C charger to SensorBox. Make sure to shutdown the Sensorbox properly from the operating system (do not just switch off the power).

To set up the SensorBox from a host computer, connect a USB port on the host computer with a USB cable (https://www.amazon.com/gp/product/B00HSS9L6G/ref=ppx_yo_dt_b_asin_title_o04_s00?ie=UTF8&psc=1) to the USB Keystone Jack in the SensorBox.

aiWerkstatt (http://www.aiwerkstatt.com/)TM SensorBoxTM v1.0 9/9
