AIWerkstatt/SensorBox/4-Setup/sw/NVIDIA_Jetson_Xavier_NX/Intel_RealSense_D435i/librealsense/wrappers/python/examples/box_dimensioner_multicam/samplesetupandoutput.jpg

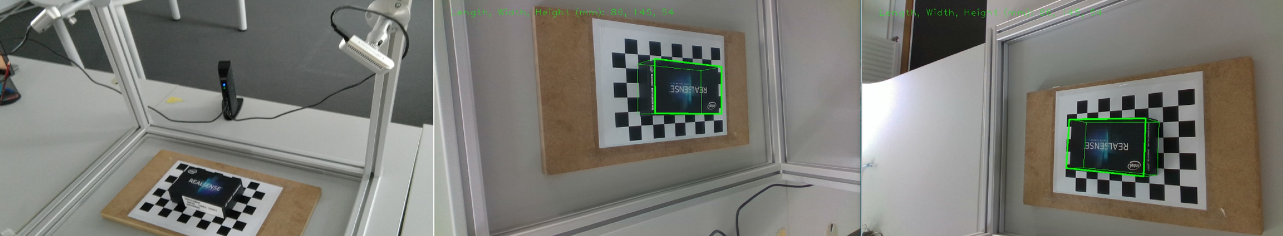
4-Setup/sw/NVIDIA_Jetson_Xavier_NX/Intel_RealSense_D435i/librealsense/wrappers/python/examples/box_dimensioner_multicam/samplesetupandoutput.jpg
