AIWerkstatt/SensorBox/4-Setup/sw/SparkFun_RedBoard_Turbo/ArduinoIDE/arduino-1.8.13-linux64/arduino-1.8.13/reference/www.arduino.cc/en/uploads/Guide/USBCable.jpg

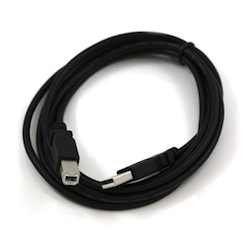
4-Setup/sw/SparkFun_RedBoard_Turbo/ArduinoIDE/arduino-1.8.13-linux64/arduino-1.8.13/reference/www.arduino.cc/en/uploads/Guide/USBCable.jpg
