AIWerkstatt/SensorBox/4-Setup/sw/SparkFun_RedBoard_Turbo/ArduinoIDE/arduino-1.8.13-linuxaarch64/arduino-1.8.13/reference/www.arduino.cc/en/uploads/Reference/arduino_uno_ethernet_pins.png

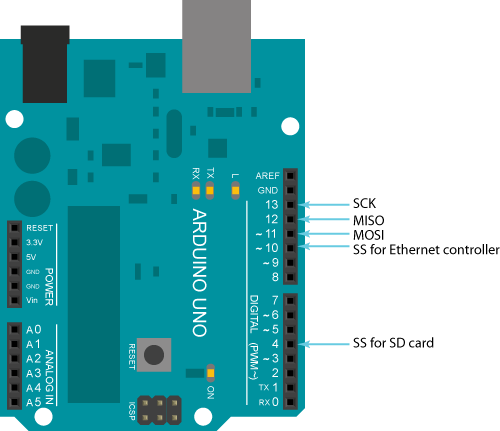
4-Setup/sw/SparkFun_RedBoard_Turbo/ArduinoIDE/arduino-1.8.13-linuxaarch64/arduino-1.8.13/reference/www.arduino.cc/en/uploads/Reference/arduino_uno_ethernet_pins.png
