AIWerkstatt/SensorBox/4-Setup/sw/SparkFun_RedBoard_Turbo/ArduinoIDE/arduino-1.8.13-linuxaarch64/arduino-1.8.13/reference/www.arduino.cc/en/uploads/Reference/bipolar_stepper_four_pins.jpg

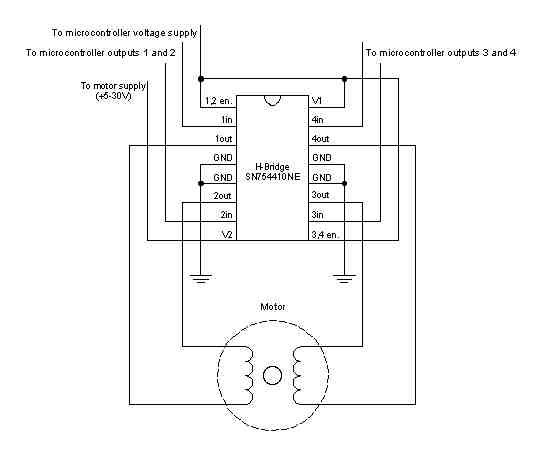
4-Setup/sw/SparkFun_RedBoard_Turbo/ArduinoIDE/arduino-1.8.13-linuxaarch64/arduino-1.8.13/reference/www.arduino.cc/en/uploads/Reference/bipolar_stepper_four_pins.jpg
